sparkfun/SparkFun_Qwiic_Human_Presence_Sensor-STHS34PF80/docs/assets/img/thumbnail.jpg

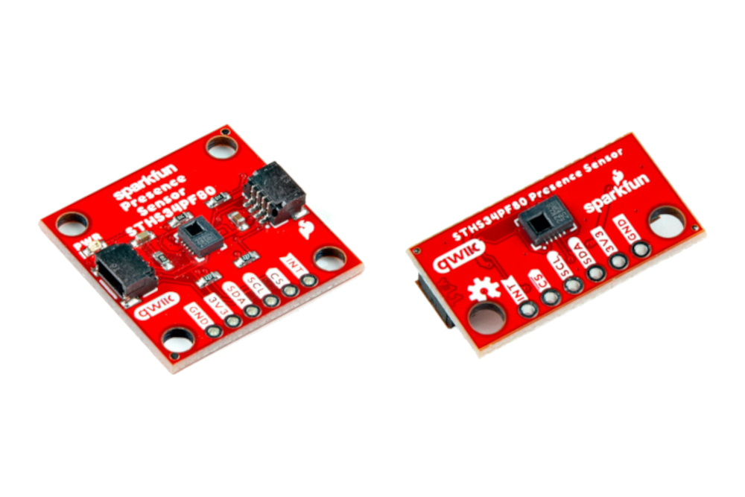
docs/assets/img/thumbnail.jpg
