sparkfun/SparkFun_Qwiic_Human_Presence_Sensor-STHS34PF80/docs/assets/img/hookup_guide/22494-bottom.png

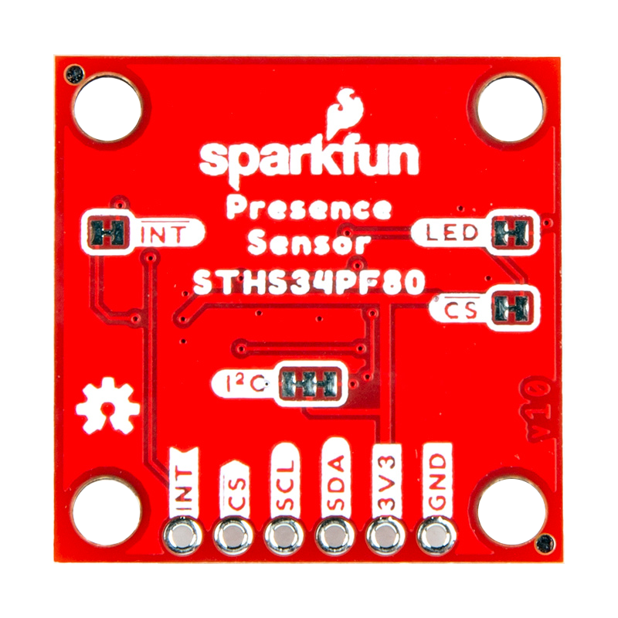
docs/assets/img/hookup_guide/22494-bottom.png
