sparkfun/SparkFun_Qwiic_Human_Presence_Sensor-STHS34PF80/docs/assets/img/hookup_guide/23253-top.png

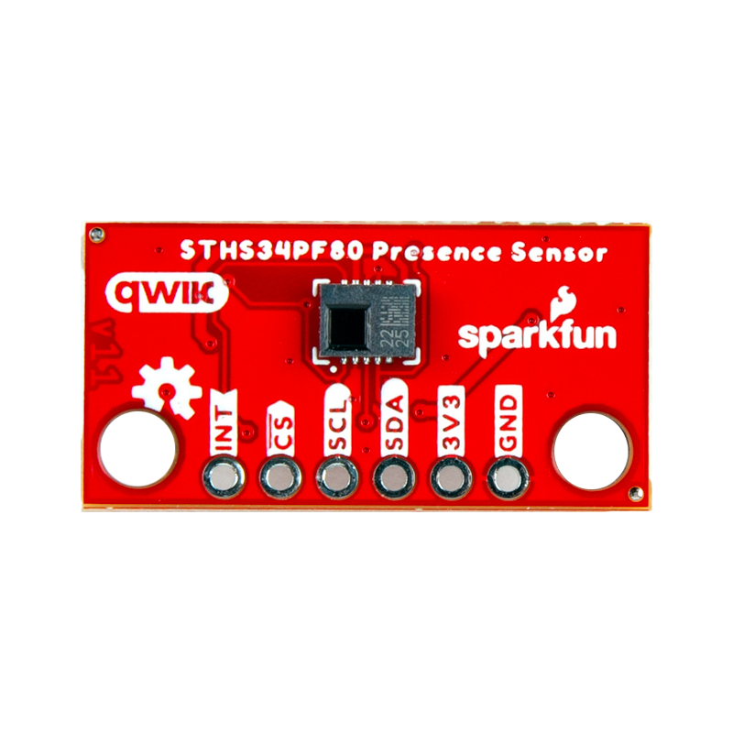
docs/assets/img/hookup_guide/23253-top.png
